Eontronics/RetroMedleyCard/Graphics/Audio_Out.png

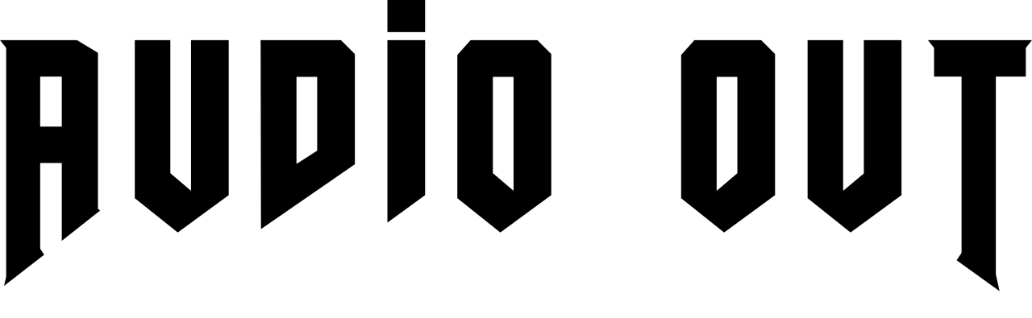
Graphics/Audio_Out.png
