Eontronics/RetroMedleyCard/Graphics/MM_Card.png

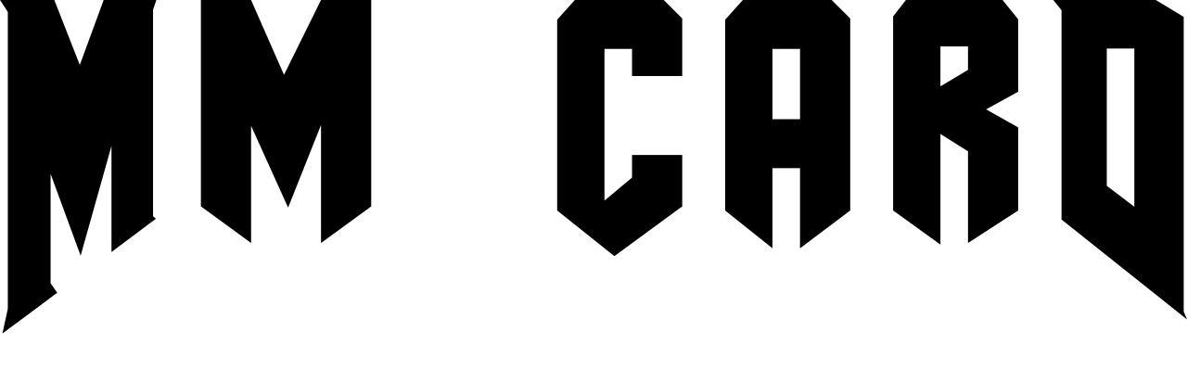
Graphics/MM_Card.png
