Eontronics/RetroMedleyCard/Graphics/RMC.png

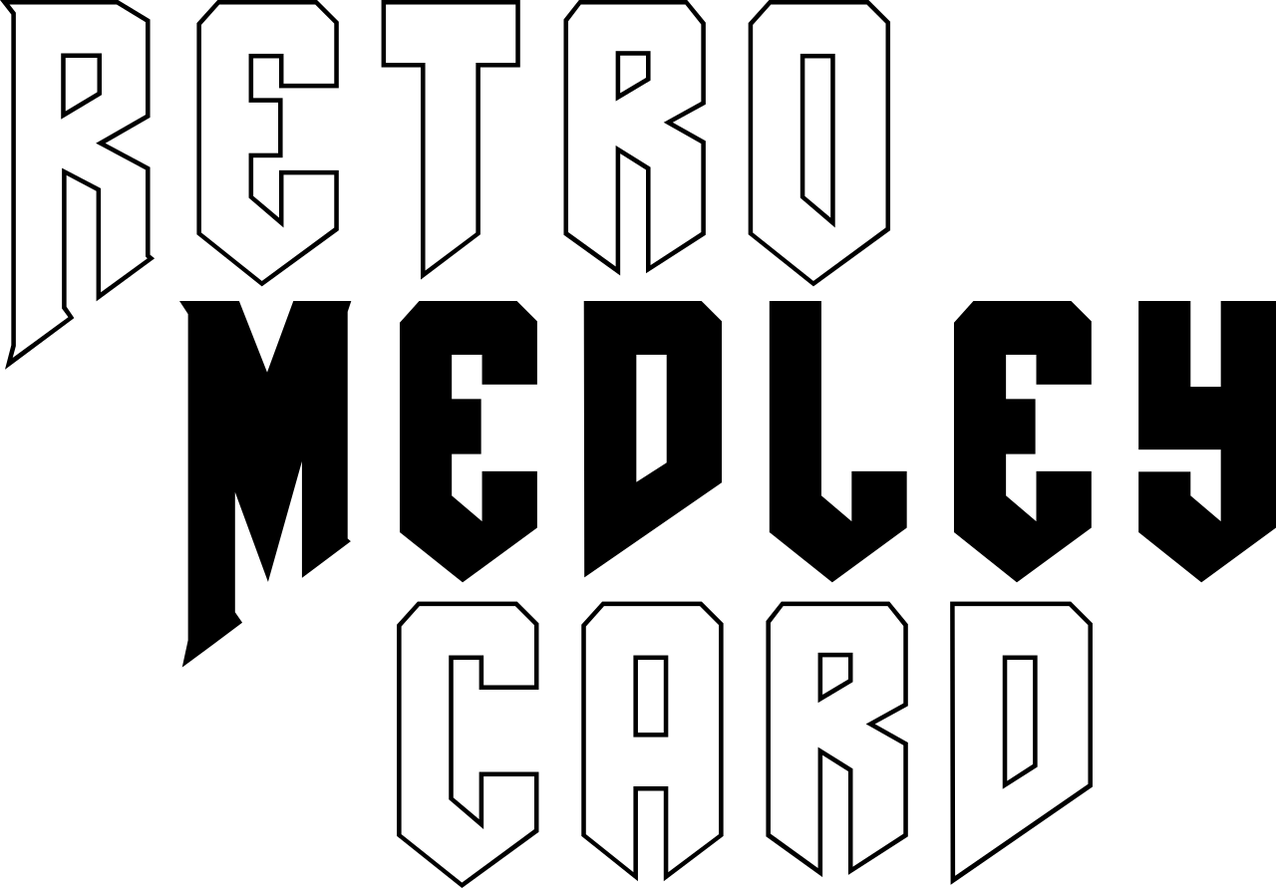
Graphics/RMC.png
