Eontronics/RetroMedleyCard/Graphics/Usb_Host.png

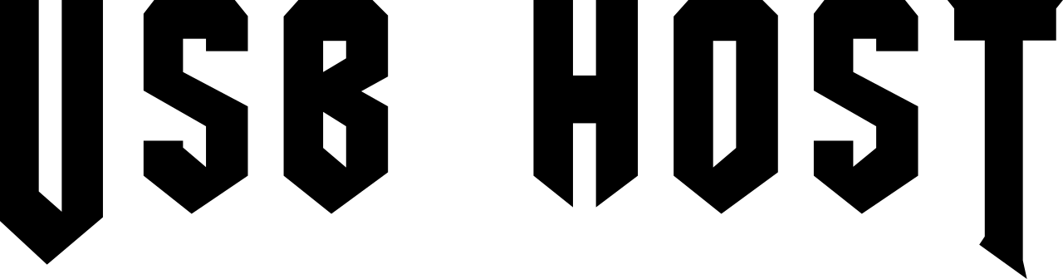
Graphics/Usb_Host.png
