Eontronics/RetroMedleyCard/Graphics/Usb_Power.png

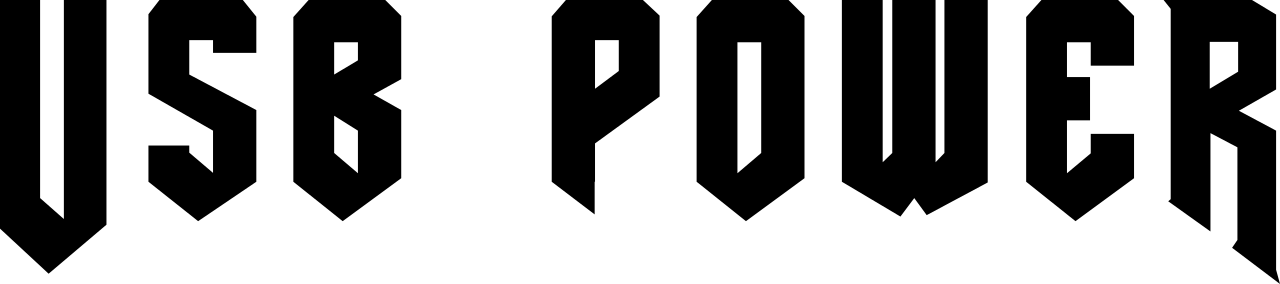
Graphics/Usb_Power.png
