Eontronics/RetroMedleyCard/Graphics/Video_Out.png

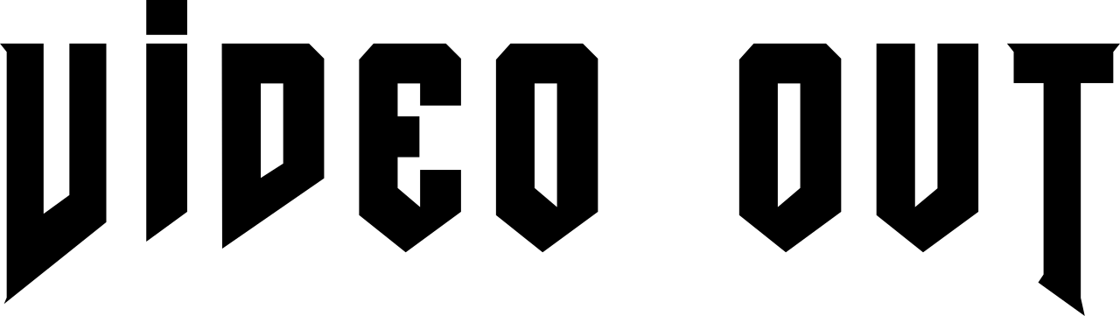
Graphics/Video_Out.png
